HasanTheSyrian/ALTAIR/Documentation/MYIR Hardware/Mechanical/images/MYC-C7Z010 20_3.png

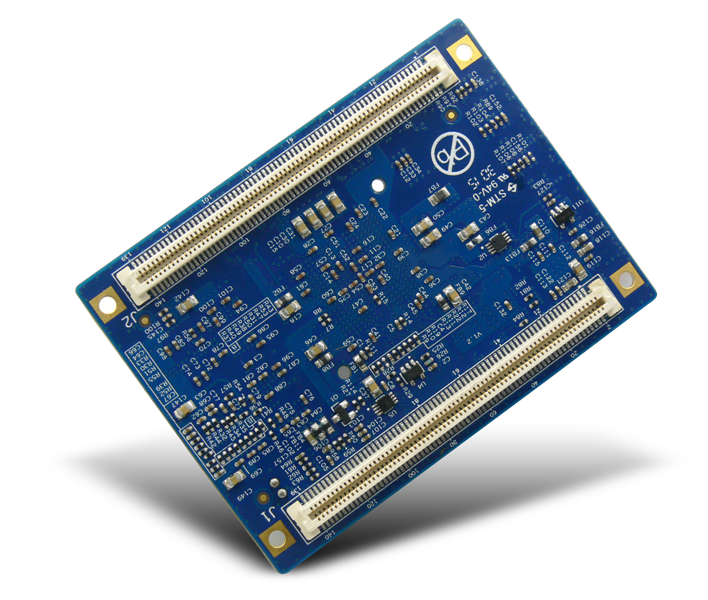
Documentation/MYIR Hardware/Mechanical/images/MYC-C7Z010 20_3.png
