HasanTheSyrian/ALTAIR/Documentation/MYIR Hardware/Mechanical/images/MYC-C7Z010_20_makt2.png

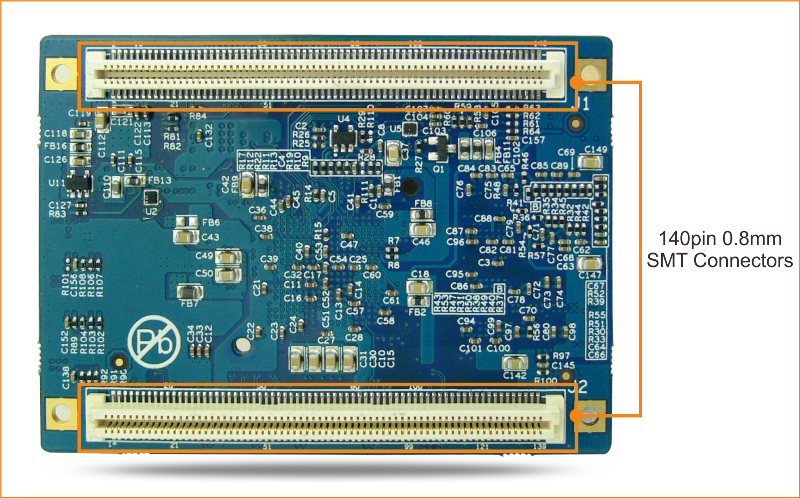
Documentation/MYIR Hardware/Mechanical/images/MYC-C7Z010_20_makt2.png
