HasanTheSyrian/ALTAIR/Documentation/MYIR Hardware/Mechanical/images/MYD-C7Z010 20_7.png

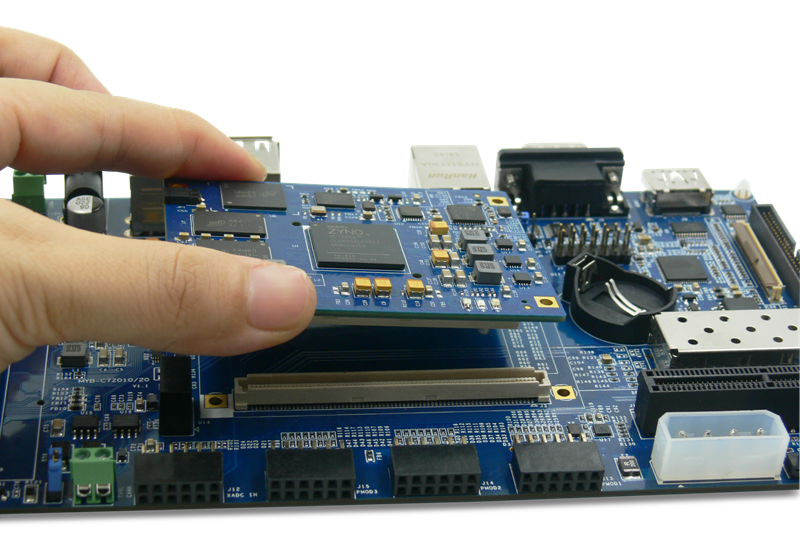
Documentation/MYIR Hardware/Mechanical/images/MYD-C7Z010 20_7.png
