HasanTheSyrian/ALTAIR/Documentation/MYIR Hardware/Mechanical/MYC-C7Z010_20-SOM-dim.pdf

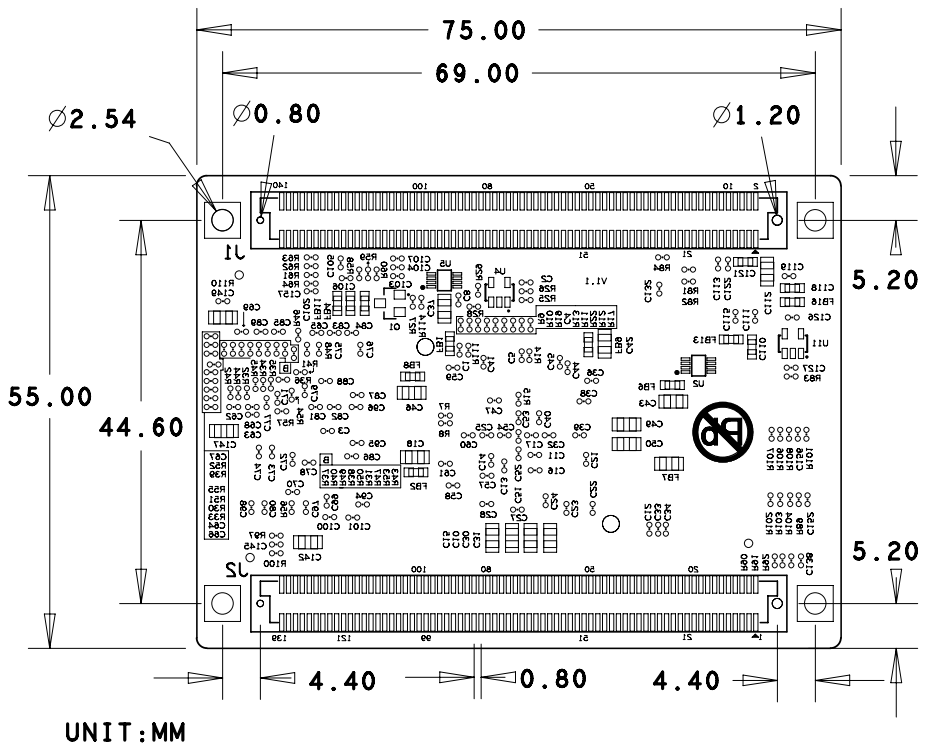
[picture p31: page 1]
